balassy/terminator-clock/_Photos/IMG_20210110_062134.jpg

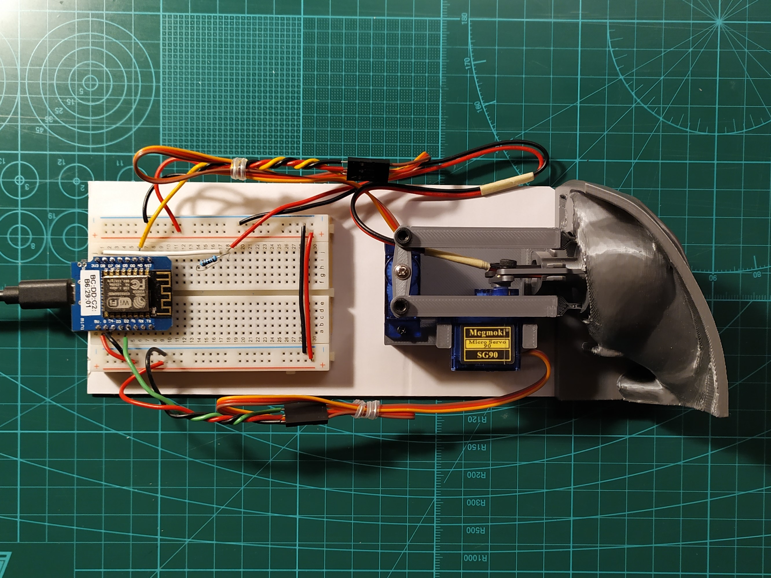
_Photos/IMG_20210110_062134.jpg
