balassy/terminator-clock/_Photos/IMG_20210110_062222.jpg

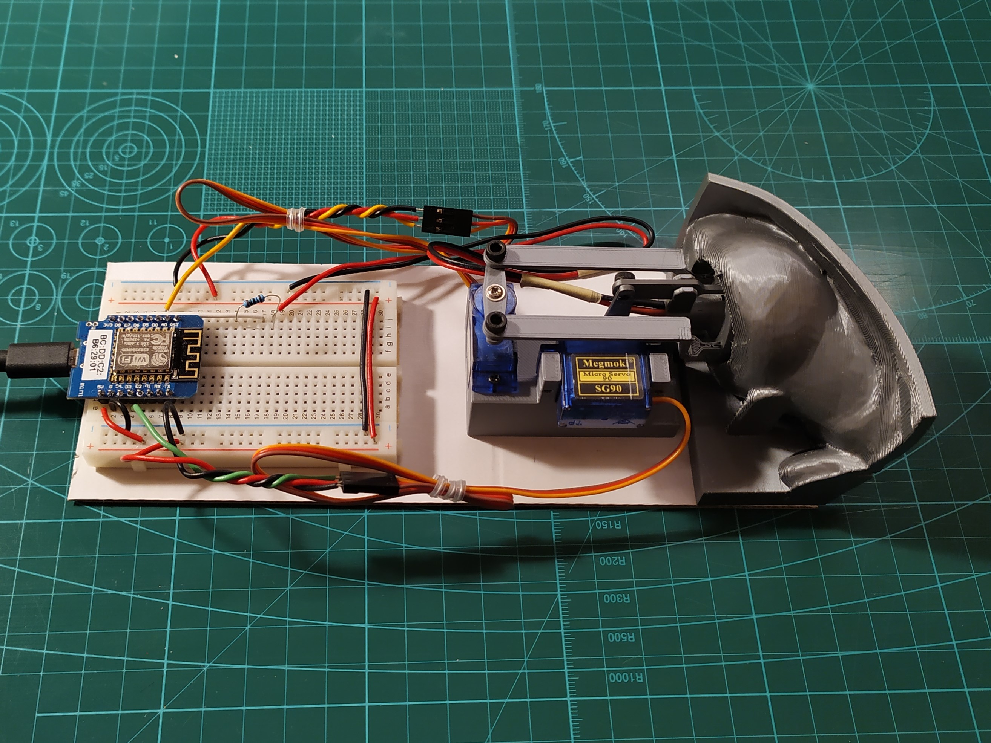
_Photos/IMG_20210110_062222.jpg
