balassy/terminator-clock/_Photos/IMG_20210110_062234.jpg

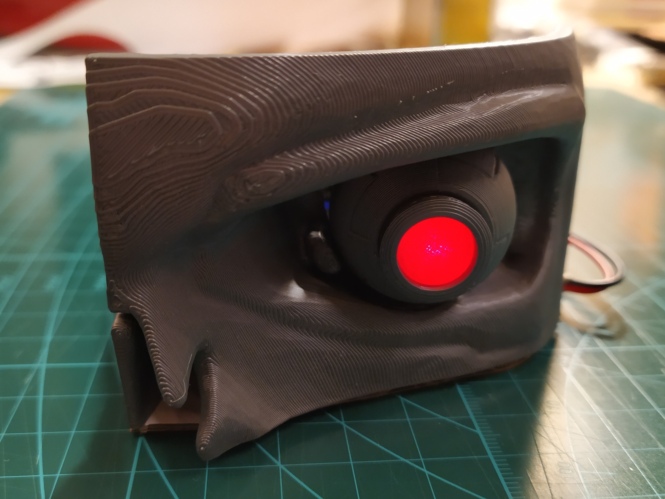
_Photos/IMG_20210110_062234.jpg
