balassy/terminator-clock/_Photos/IMG_20210110_062427_1.jpg

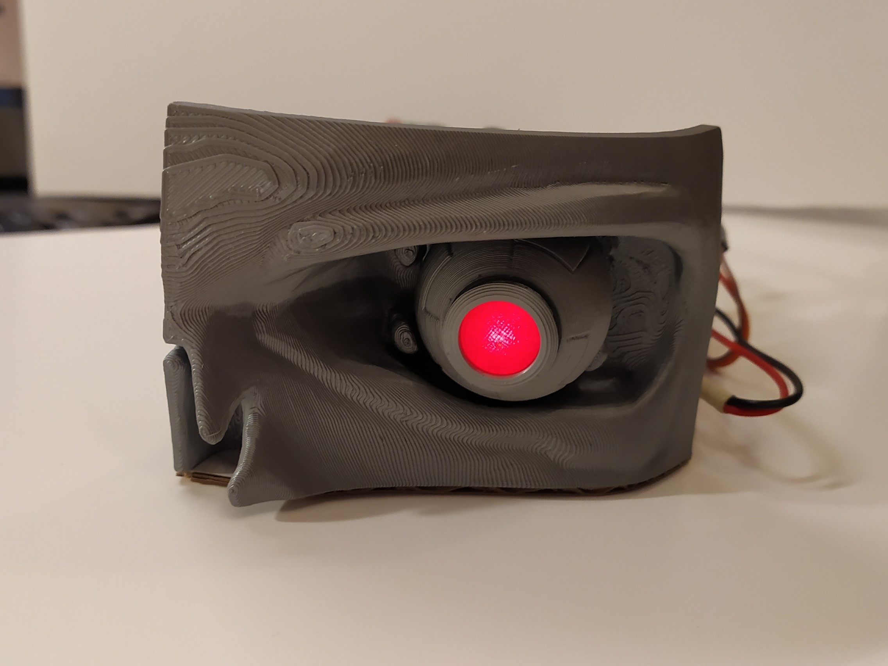
_Photos/IMG_20210110_062427_1.jpg
