balassy/terminator-clock/_Photos/IMG_20210110_062457.jpg

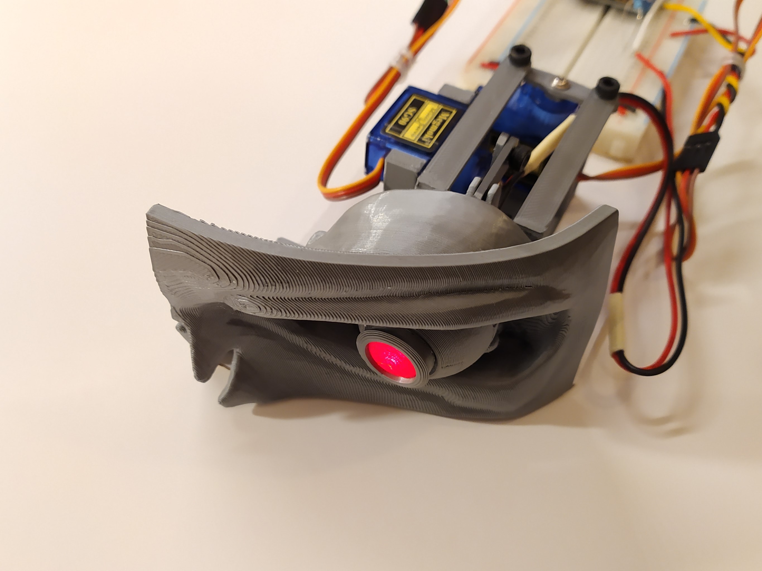
_Photos/IMG_20210110_062457.jpg
