balassy/terminator-clock/_Photos/IMG_20210110_062538.jpg

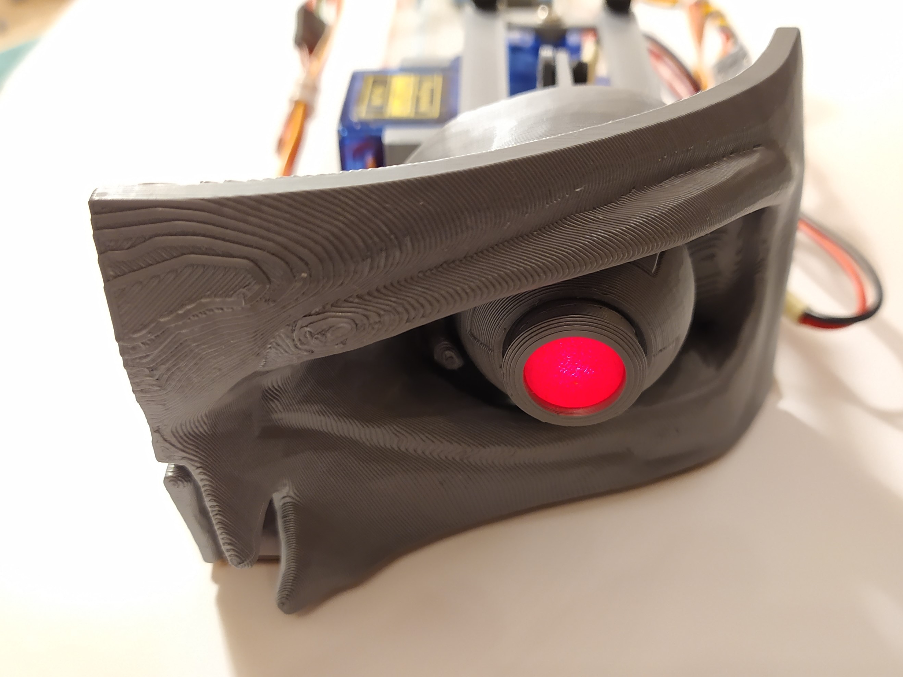
_Photos/IMG_20210110_062538.jpg
