balassy/terminator-clock/_Photos/IMG_20210110_062554.jpg

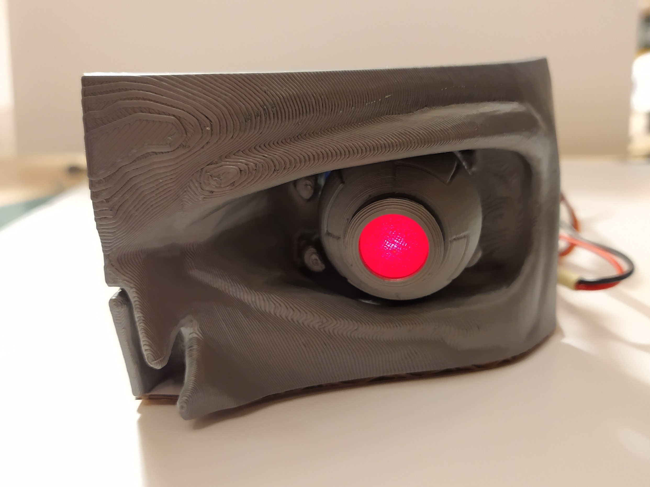
_Photos/IMG_20210110_062554.jpg
