balassy/terminator-clock/_Photos/IMG_20210110_062623.jpg

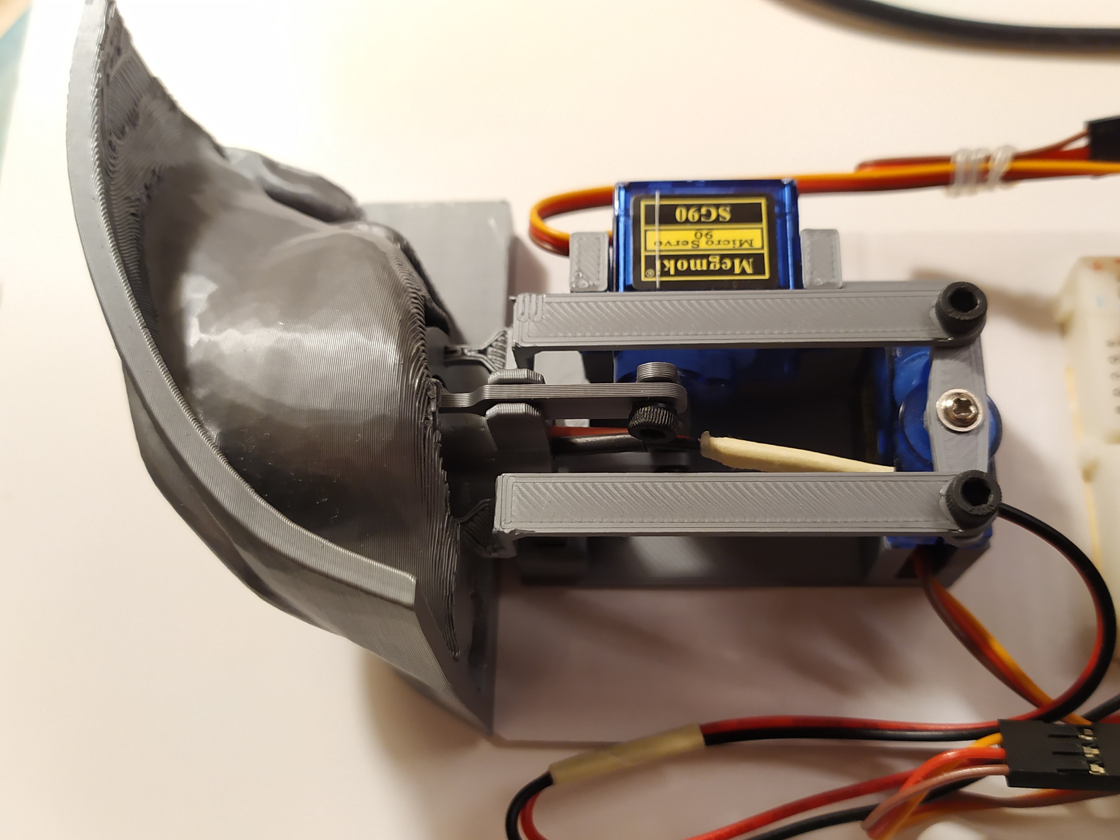
_Photos/IMG_20210110_062623.jpg
