balassy/terminator-clock/_Photos/IMG_20210110_062652_1.jpg

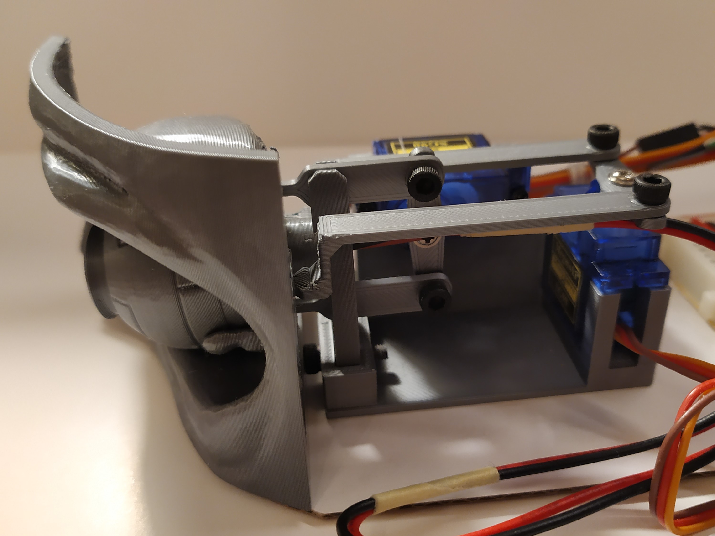
_Photos/IMG_20210110_062652_1.jpg
