balassy/terminator-clock/_Photos/IMG_20210110_062704.jpg

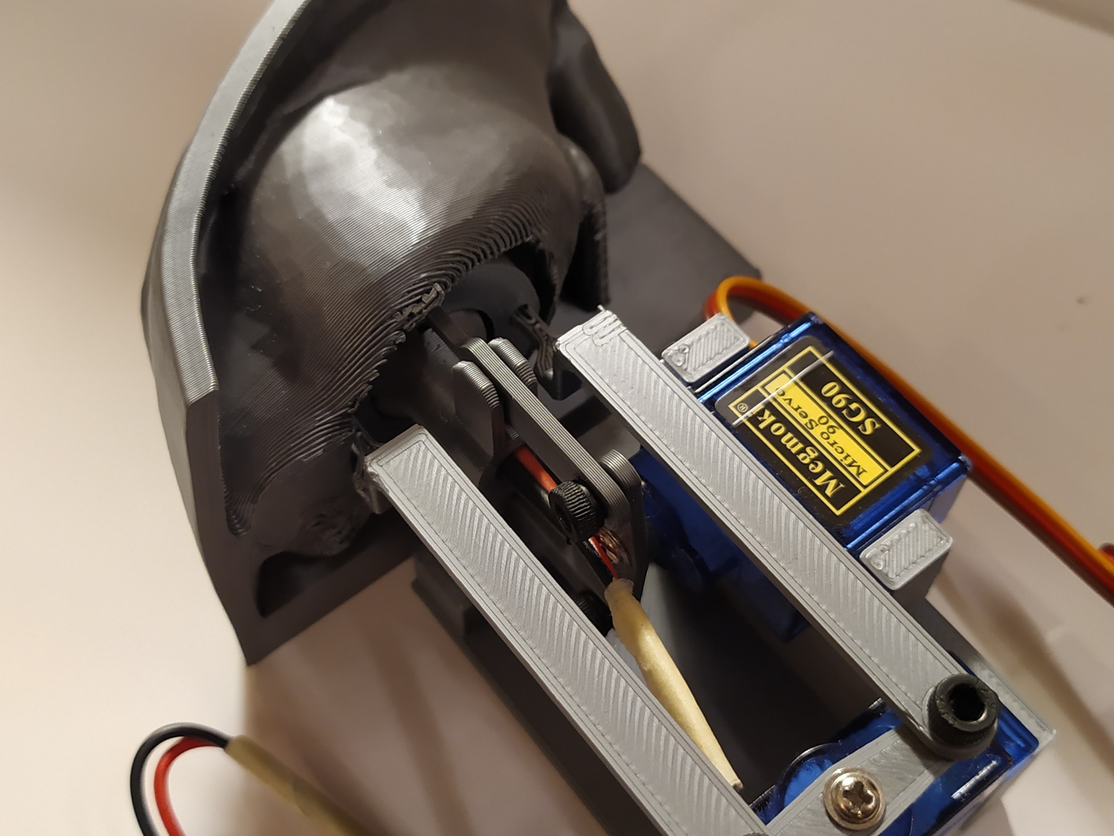
_Photos/IMG_20210110_062704.jpg
